Remote-Area-Monitoring/Remote-Area-Monitoring/3D_Models/Final_Design/wind_fin_pipeMnt.STL

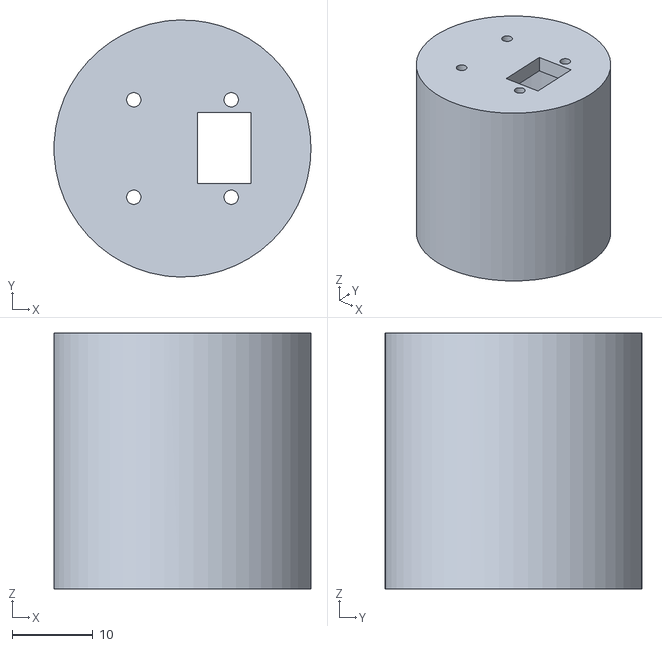
[picture p15: CAD file, 2022-09-11]
3D_Models/Final_Design/wind_fin_pipeMnt.STL
31.9 x 31.9 x 31.8
