Remote-Area-Monitoring/Remote-Area-Monitoring/3D_Models/Final_Design/aggregator_bottom.STL

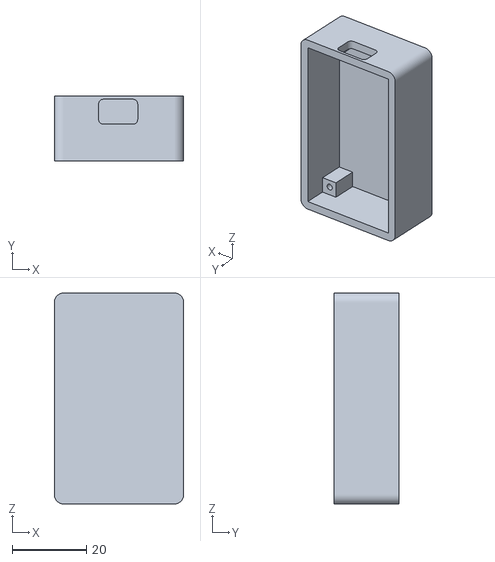
[picture p16: CAD file, 2022-09-11]
3D_Models/Final_Design/aggregator_bottom.STL
34.9 x 17.5 x 56.9
