Remote-Area-Monitoring/Remote-Area-Monitoring/3D_Models/Final_Design/cap2mag.STL

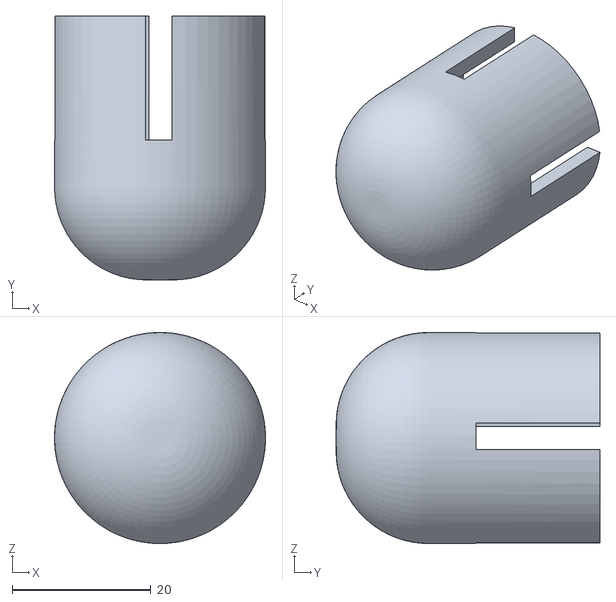
[picture p17: CAD file, 2022-09-11]
3D_Models/Final_Design/cap2mag.STL
30.5 x 38.1 x 30.5
