Remote-Area-Monitoring/Remote-Area-Monitoring/3D_Models/Final_Design/aggregator_top.STL

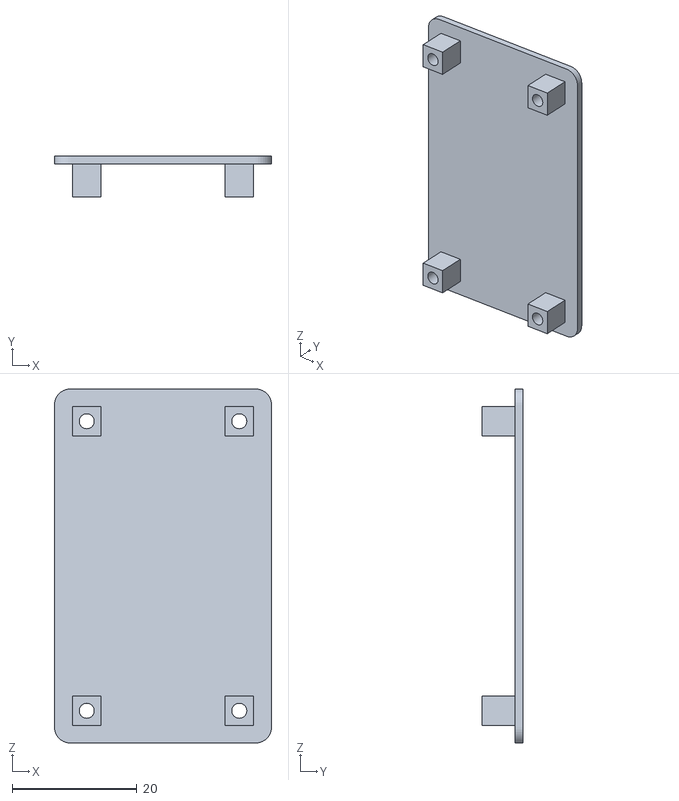
[picture p18: CAD file, 2022-09-11]
3D_Models/Final_Design/aggregator_top.STL
34.9 x 6.58 x 56.9
