Remote-Area-Monitoring/Remote-Area-Monitoring/3D_Models/Final_Design/lens_bezel.STL

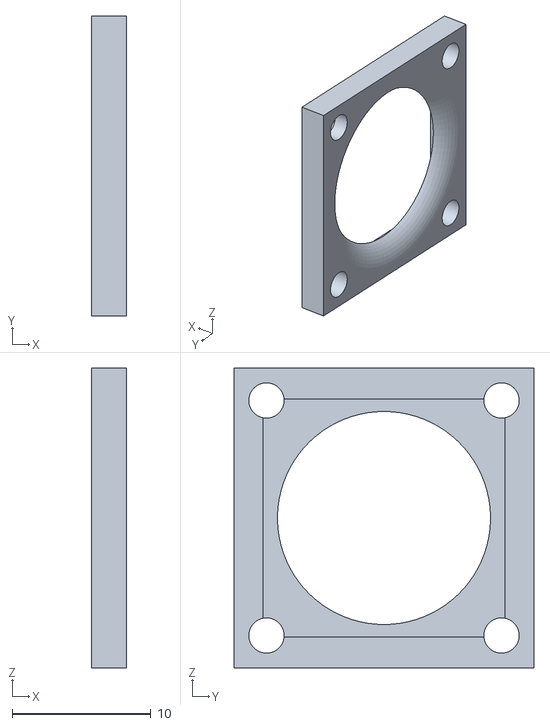
[picture p19: CAD file, 2022-09-11]
3D_Models/Final_Design/lens_bezel.STL
2.54 x 21.6 x 21.6
