Remote-Area-Monitoring/Remote-Area-Monitoring/3D_Models/Final_Design/an_fin_mount.STL

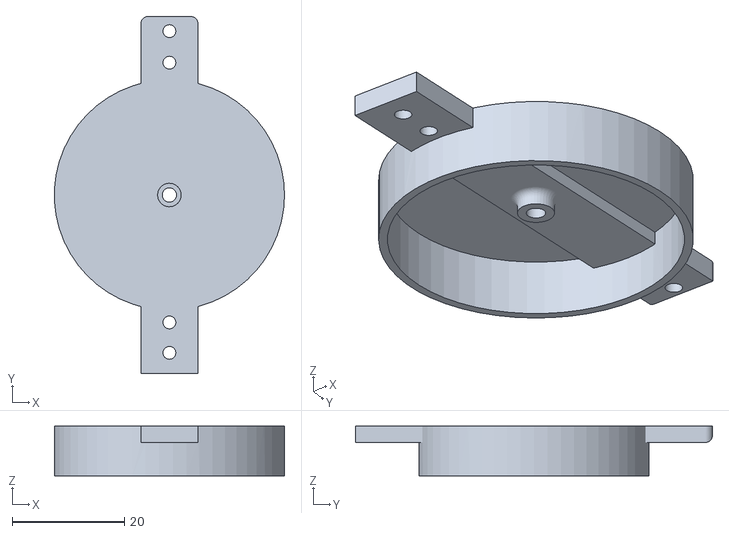
[picture p20: CAD file, 2022-09-11]
3D_Models/Final_Design/an_fin_mount.STL
40.9 x 63.5 x 8.89
