Remote-Area-Monitoring/Remote-Area-Monitoring/3D_Models/Final_Design/wind_fin_bearing.STL

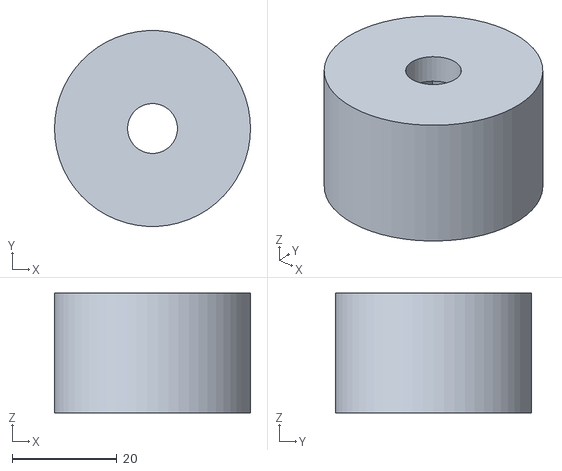
[picture p21: CAD file, 2022-09-11]
3D_Models/Final_Design/wind_fin_bearing.STL
37.4 x 37.3 x 22.9
