Remote-Area-Monitoring/Remote-Area-Monitoring/3D_Models/Final_Design/Part2^anemometer.STL

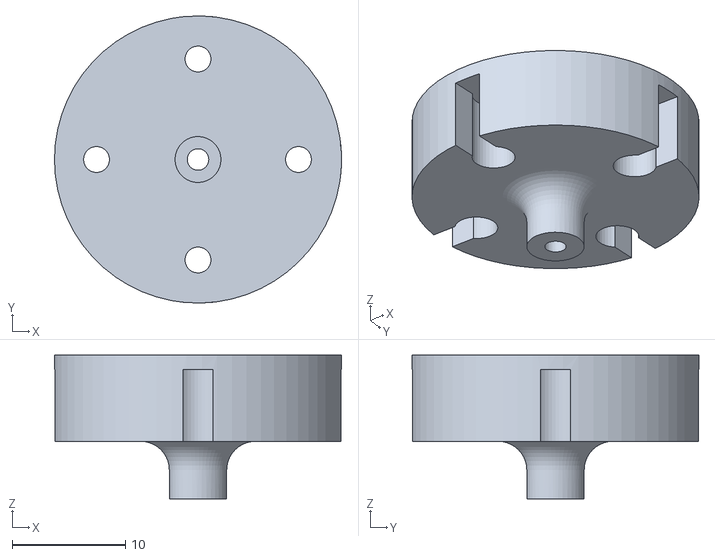
[picture p22: CAD file, 2022-09-11]
3D_Models/Final_Design/Part2^anemometer.STL
25.4 x 25.4 x 12.7
