Remote-Area-Monitoring/Remote-Area-Monitoring/3D_Models/Final_Design/solar bracket.STL

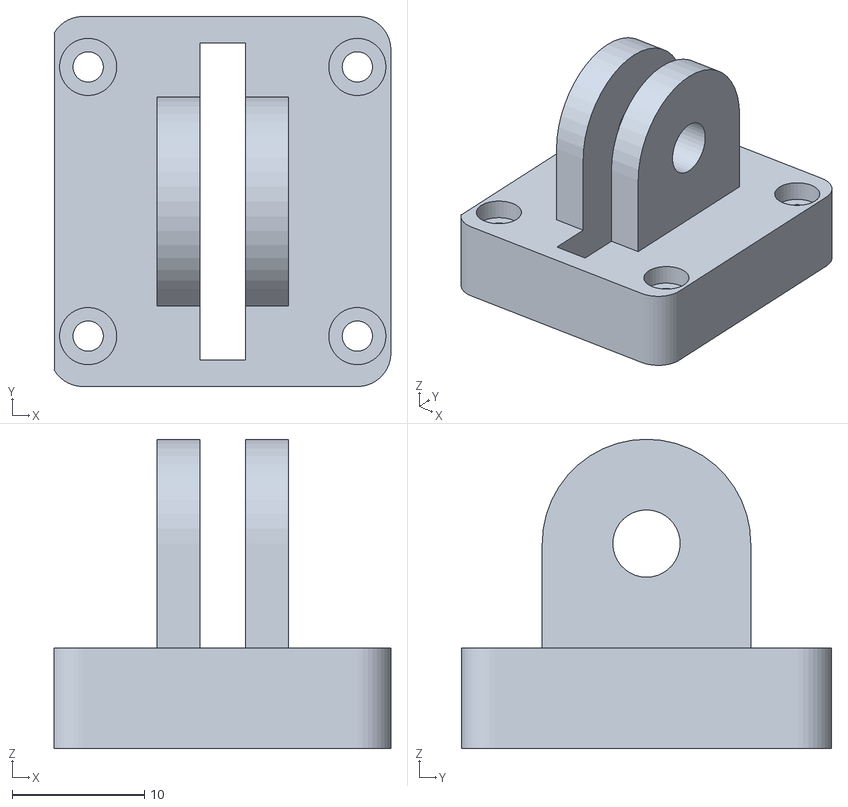
[picture p23: CAD file, 2022-09-11]
3D_Models/Final_Design/solar bracket.STL
25.4 x 27.9 x 23.4
