Remote-Area-Monitoring/Remote-Area-Monitoring/3D_Models/Final_Design/fin spacer.STL

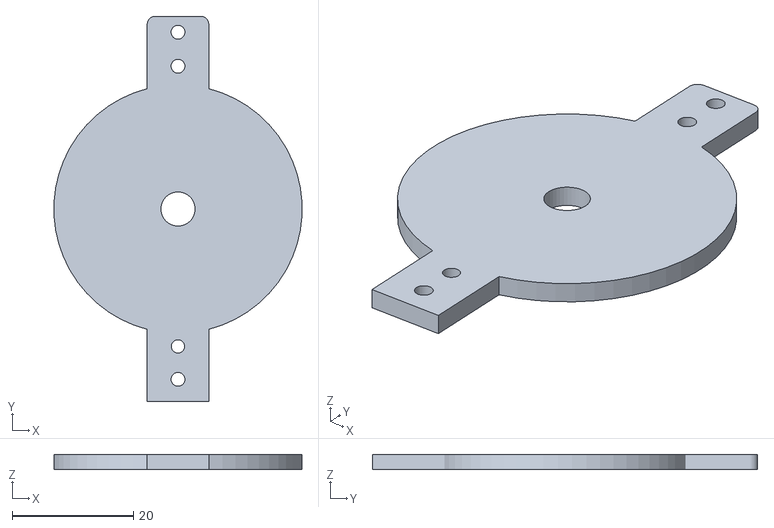
[picture p24: CAD file, 2022-09-11]
3D_Models/Final_Design/fin spacer.STL
40.9 x 63.5 x 2.54
