Remote-Area-Monitoring/Remote-Area-Monitoring/3D_Models/Final_Design/bottom_grill.STL

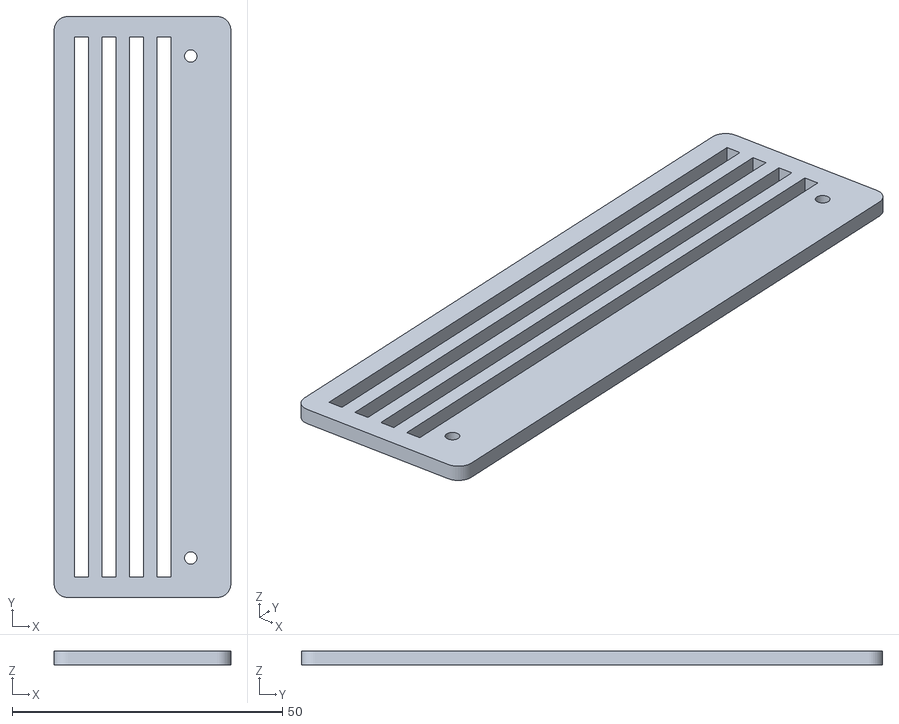
[picture p26: CAD file, 2022-09-11]
3D_Models/Final_Design/bottom_grill.STL
32.7 x 107.4 x 2.54
