Remote-Area-Monitoring/Remote-Area-Monitoring/3D_Models/Final_Design/pvcPipe mount.STL

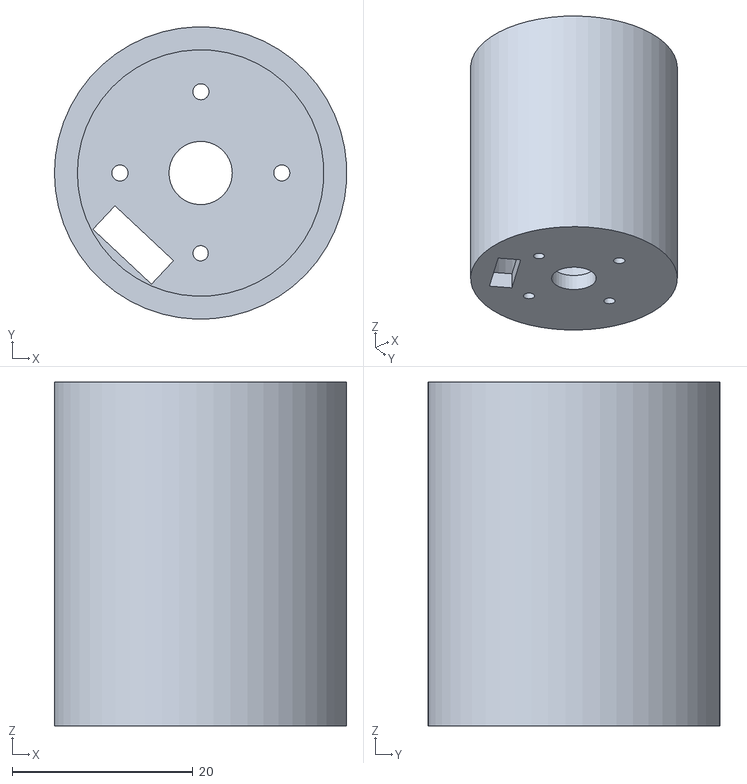
[picture p27: CAD file, 2022-09-11]
3D_Models/Final_Design/pvcPipe mount.STL
32.4 x 32.4 x 38.1
