Remote-Area-Monitoring/Remote-Area-Monitoring/3D_Models/Final_Design/Copy of Part1^anemometer rev4.STL

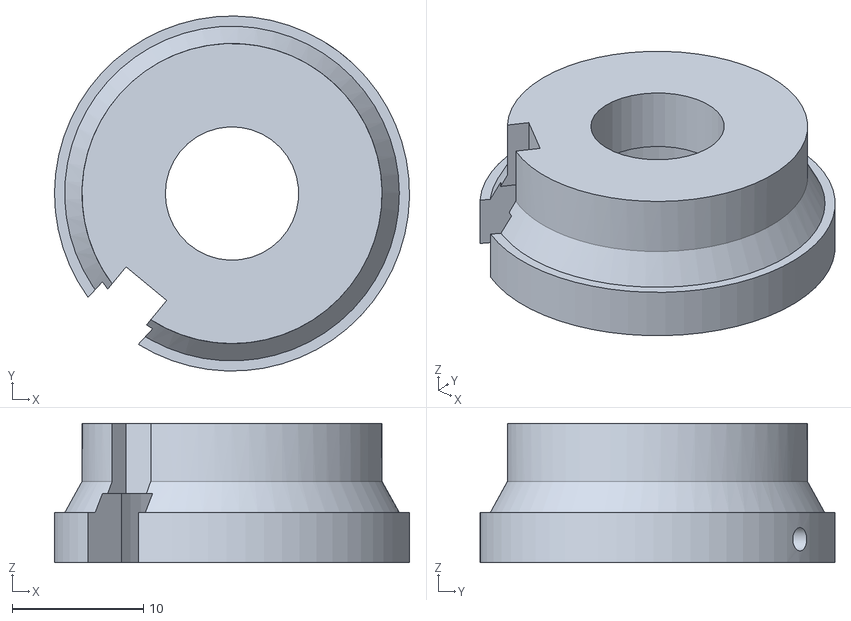
[picture p28: CAD file, 2022-09-11]
3D_Models/Final_Design/Copy of Part1^anemometer rev4.STL
27.0 x 27.0 x 10.6
