Remote-Area-Monitoring/Remote-Area-Monitoring/3D_Models/Final_Design/Part6^anemometer.STL

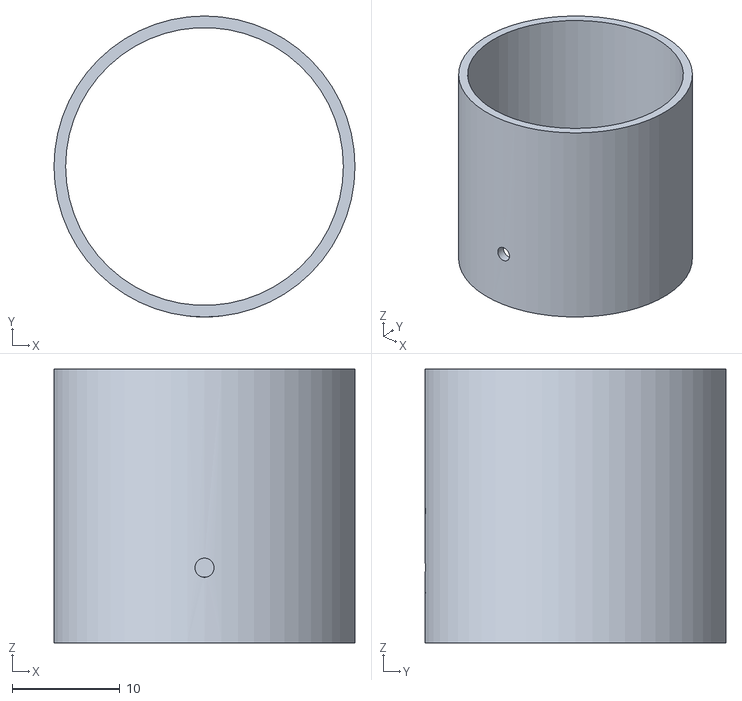
[picture p29: CAD file, 2022-09-11]
3D_Models/Final_Design/Part6^anemometer.STL
27.9 x 27.9 x 25.4
