Remote-Area-Monitoring/Remote-Area-Monitoring/3D_Models/Final_Design/top.STL

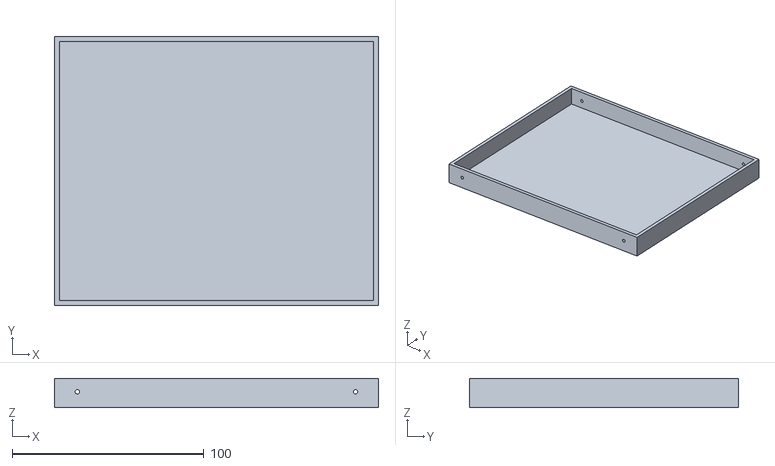
[picture p30: CAD file, 2022-09-11]
3D_Models/Final_Design/top.STL
169.0 x 140.2 x 15.2
