Remote-Area-Monitoring/Remote-Area-Monitoring/3D_Models/Final_Design/Part6^anemo rev3.STL

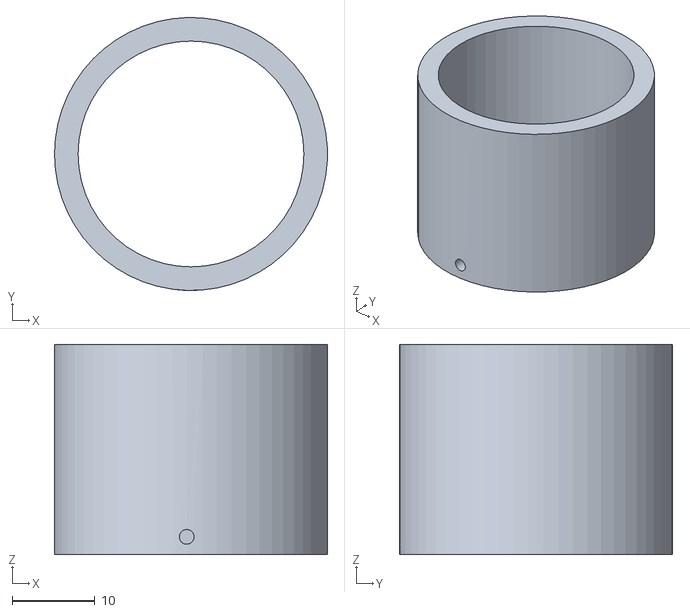
[picture p31: CAD file, 2022-09-11]
3D_Models/Final_Design/Part6^anemo rev3.STL
33.0 x 33.0 x 25.4
