Remote-Area-Monitoring/Remote-Area-Monitoring/3D_Models/Final_Design/wind_speed_cup.STL

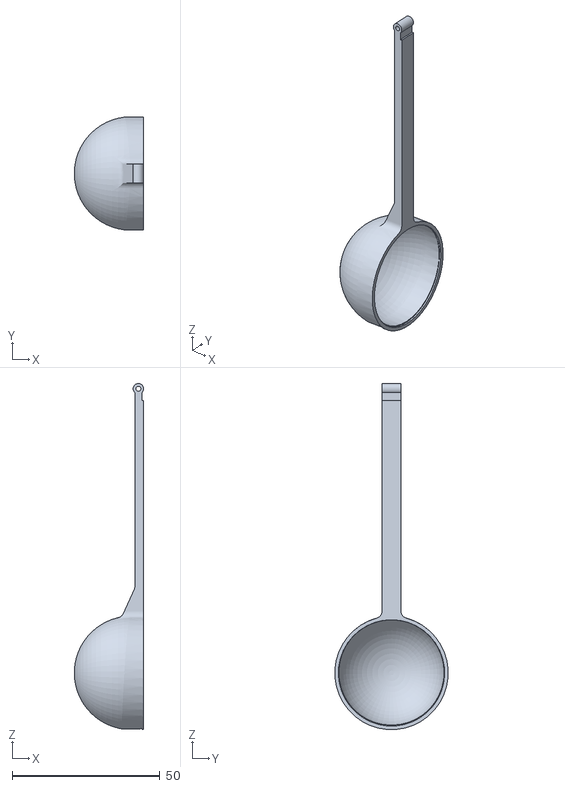
[picture p32: CAD file, 2022-09-11]
3D_Models/Final_Design/wind_speed_cup.STL
23.4 x 38.3 x 116.9
