Remote-Area-Monitoring/Remote-Area-Monitoring/3D_Models/Final_Design/solar_frame.STL

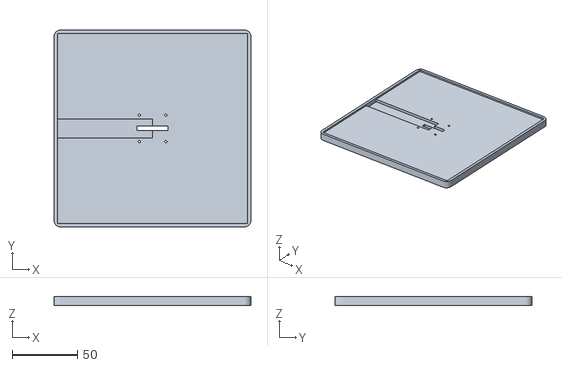
[picture p33: CAD file, 2022-09-11]
3D_Models/Final_Design/solar_frame.STL
150.9 x 150.9 x 6.65
