Remote-Area-Monitoring/Remote-Area-Monitoring/3D_Models/Final_Design/box bottom.STL

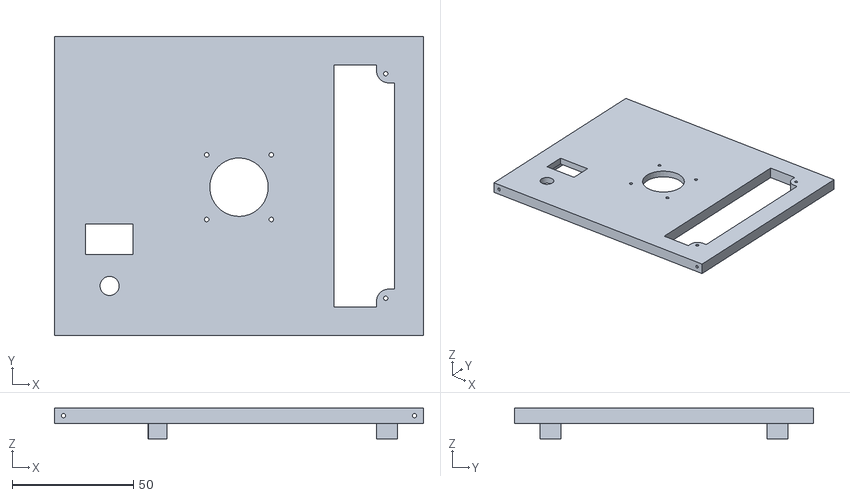
[picture p34: CAD file, 2022-09-11]
3D_Models/Final_Design/box bottom.STL
152.5 x 123.7 x 12.7
