Remote-Area-Monitoring/Remote-Area-Monitoring/3D_Models/Final_Design/Top_box.STL

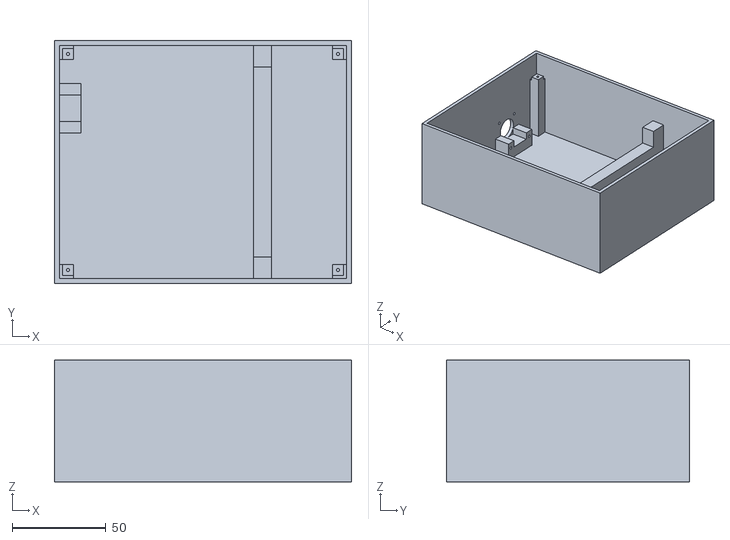
[picture p35: CAD file, 2022-09-11]
3D_Models/Final_Design/Top_box.STL
158.2 x 129.4 x 64.8
