Remote-Area-Monitoring/Remote-Area-Monitoring/source/prototype/current_monitor_mesh/current_monitor_aggregator/current_monitor_aggregator.ino

#include <painlessMesh.h>

#define   MESH_PREFIX     "ram"
#define   MESH_PASSWORD   "SeniorDesign1"
#define   MESH_PORT       5555


Scheduler userScheduler;
painlessMesh mesh;

void sendMessage();

Task taskSendMessage(TASK_SECOND * 1, TASK_FOREVER, &sendMessage);

void sendMessage()
{
  String message = "Echo sent from aggregator. Aggregator ID: ";
  message += mesh.getNodeId();
  mesh.sendBroadcast(message);
  // mesh.sendSingle(8043016, message);
  taskSendMessage.setInterval(TASK_SECOND * 10);
}

// Needed for painless library
void receivedCallback( uint32_t from, String &msg ) {
  Serial.printf("%s\n", msg.c_str());
}

void newConnectionCallback(uint32_t nodeId) {
    Serial.printf("--> startHere: New Connection, nodeId = %u\n", nodeId);
}

void changedConnectionCallback() {
  Serial.printf("Changed connections\n");
}

void nodeTimeAdjustedCallback(int32_t offset) {
    Serial.printf("Adjusted time %u. Offset = %d\n", mesh.getNodeTime(),offset);
}

void setup() {
  Serial.begin(115200);

//mesh.setDebugMsgTypes( ERROR | MESH_STATUS | CONNECTION | SYNC | COMMUNICATION | GENERAL | MSG_TYPES | REMOTE ); // all types on
  mesh.setDebugMsgTypes( ERROR | STARTUP );  // set before init() so that you can see startup messages

  mesh.init( MESH_PREFIX, MESH_PASSWORD, &userScheduler, MESH_PORT );
  mesh.onReceive(&receivedCallback);
  mesh.onNewConnection(&newConnectionCallback);
  mesh.onChangedConnections(&changedConnectionCallback);
  mesh.onNodeTimeAdjusted(&nodeTimeAdjustedCallback);

  userScheduler.addTask( taskSendMessage );
  taskSendMessage.enable();
}

void loop() {
  // it will run the user scheduler as well
  mesh.update();
}
