Remote-Area-Monitoring/Remote-Area-Monitoring/source/network/mesh.py

import serial
from serial import Serial
import json
import time
from source.util.timekeeper import Timestamps
from source.util.database import Database
from source.util.settings import Settings
from source.util.image import Image
import re
import sys
from time import sleep
from source.util.sun import Sunlight
from source.util.conversions import Convert


class Mesh:
    def __init__(self):
        self.ts = Timestamps()
        self.sun = Sunlight()
        self.image = Image()
        self.convert = Convert()
        self.config = Settings('general.config')
        self.nodes_config = Settings('nodes.config')
        self.nodes_db = Database(self.config.get_setting('databases', 'nodes_db_path'))
        self.sensor_data_db = Database(self.config.get_setting('databases', 'sensor_data_db_path'))
        self.images_db = Database(self.config.get_setting('databases', 'images_database_path'))
        self.port = self.config.get_setting('mesh_network', 'port')
        self.baud = self.config.get_int_setting('mesh_network', 'baud_rate')
        self.serial_timeout = self.config.get_int_setting('mesh_network', 'serial_timeout')
        self.ts = Timestamps()
        self.port = self.__get_connection()
        self.network_connection = self.is_connected()

    def __get_connection(self):
        # TODO: Move first try block to a function to check connection for any OS
        print(self.port)
        try:
            return Serial(self.port, self.baud, timeout=self.serial_timeout)
        except serial.SerialException:
            print('Windows COM port not found')
        try:
            return Serial('/dev/tty.usbserial-0001', self.baud, timeout=self.serial_timeout)
        except serial.SerialException:
            print('Mac COM port not found')
        print('No COM Ports Found')
        return None

    def get_topology(self):
        self.port.write('{"node_id":0, "message":"None"}'.encode())
        data = self.receive_json()
        if data is None:
            return data
        elif 'nodeId' not in data:
            data = self.receive_json()
        if data is None:
            return data
        if 'nodeId' not in data:
            return None
        # print(data)
        return data

    def get_connection_strength(self):
        self.port.write('{"node_id":2, "message":"None"}'.encode())
        data = self.receive_json()
        if data is None:
            return data
        elif 'connection_strength' not in data:
            data = self.receive_json()
        if data is None:
            return data
        if 'connection_strength' not in data:
            return None
        # print(data)
        return data

    def list_connected_nodes(self):
        topo = self.get_topology()
        # topo = {'nodeId': 2222635529, 'subs': [{'nodeId': 2222631473, 'subs': [{'nodeId': 2222817205}]}]}
        if topo is None:
            return None
        elif 'subs' not in topo:
            return None
        # nodes = list()
        topo.pop('nodeId')
        topo = json.dumps(topo)
        nodes = re.findall(r'\d+', topo)
        int_nodes = list()
        for node in nodes:
            try:
                int_nodes.append(int(node))
            except Exception as e:
                print('Invalid Node ID: ', node)
                print(e)
        return int_nodes

    def is_connected(self):
        if self.port is None:
            print('No com port found - not connected')
            return False
        startup = time.time()
        while True:
            topo = self.get_topology()
            if topo is not None:
                if 'subs' in topo:
                    return True
            if time.time() - startup > self.config.get_int_setting('mesh_network', 'connection_timeout'):
                print("TIMEOUT ERROR: Node Failed to Connect to Mesh")
                return False

    def send(self, node_id, message):
        msg = {'node_id': node_id, 'message': message}
        msg = json.dumps(msg).encode()
        self.port.write(msg)

    def receive_json(self):
        timeout = self.config.get_int_setting('mesh_network', 'receive_timeout')
        start = self.ts.get_timestamp()
        while True:
            if self.ts.get_timestamp() - start > timeout:
                return None
            try:
                message = self.port.readline()
                message = message.decode().split('*')[0]
                if '{' in message and '}' in message:
                    # print(message)
                    data = json.loads(message)
                    return data
            except Exception as e:
                print(e)
                continue

    def get_sensor_data(self, node_id):
        self.send(node_id, 'sensor_data')
        data = self.receive_json()
        if data is None:
            return data
        elif 'bus_voltage_V' not in data:
            data = self.receive_json()
        if data is None:
            return data
        elif 'bus_voltage_V' not in data:
            return None
        if 'wind_speed_raw' in data:
            data['wind_speed_mph'] = self.convert.raw_wind_speed_to_mph(data['wind_speed_raw'])
        elif 'wind_speed_mph' in data:
            if data['wind_speed_mph'] > 260:
                data['wind_speed_mph'] = 0
        if 'wind_direction_raw' in data:
            data['wind_direction'] = self.convert.raw_wind_direction_to_degrees(data['wind_direction_raw'])
        elif 'wind_direction' in data:
            if data['wind_direction'] > 360:
                data['wind_direction'] = 0
        if 'co2_ppm' in data:
            if data['co2_ppm'] < 400:
                data['co2_ppm'] = 400
        data_with_timestamp = {'timestamp': self.ts.get_timestamp()}
        data_with_timestamp.update(data)
        return data_with_timestamp

    def update_nodes_sensor_data(self):
        polling_enable = self.config.get_bool_setting('mesh_network', 'sensor_polling')
        sensors_last_updated = self.nodes_config.get_float_setting('connected_nodes', 'sensors_last_updated')
        sensors_polling_interval = self.config.get_float_setting('mesh_network', 'sensor_polling_interval')
        if polling_enable is False:
            print('Sensor Polling Disabled')
            return None
        elif self.ts.get_timestamp() - sensors_last_updated < sensors_polling_interval:
            return None
        self.nodes_config.set_setting('connected_nodes', 'sensors_last_updated', str(self.ts.get_timestamp()))
        print(self.get_topology())
        records = list()
        nodes = self.nodes_db.get_all()
        for node in nodes:
            connected_nodes = self.list_connected_nodes()
            if connected_nodes is None or len(connected_nodes) < 1:
                print('No nodes connected')
                continue
            if node['node_id'] not in connected_nodes:
                print('Node {} Not Connected'.format(node['node_id']))
                continue
            if node['status'] == 'active' and node['node_config']['sensors'] is True:
                data = self.get_sensor_data(node['node_id'])
                if data is not None:
                    print(data)
                    records.append(data)
                else:
                    # TODO: record error when node data is not found
                    print('Error: No data available for node', node['node_id'])
        self.sensor_data_db.insert_multiple(records)

    def receive_pixel_packets(self):
        # interesting note: The number of packets has no effect on the transfer speed, only the amount of data
        timeout = self.config.get_int_setting('mesh_network', 'image_timeout')
        start = self.ts.get_timestamp()
        packets = list()
        total_packets = None
        while True:
            if self.ts.get_timestamp() - start > timeout:
                return None
            try:
                raw_packets = self.port.readall()
                packets = raw_packets.decode()
                # print(packets)
                packets = packets.split('*')
                # for packet in packets:
                #     print(packet)
                data = list()
                packet_info = dict()
                for packet in packets:
                    try:
                        packet_data = json.loads(packet)
                    except Exception as e:
                        # print('failed to load json')
                        continue
                    if 'pixels' in packet_data:
                        # print(len(packet_data['pixels']))
                        data.append(packet_data)
                    elif 'total_packets_sent' in packet_data:
                        total_packets = packet_data['total_packets_sent']
                        packet_info = packet_data
                        print(packet_data)
                        print(total_packets)
                        print(len(data))
                        break
                if total_packets is not None:
                    if len(data) == (total_packets + 1):
                        print('All Packets Received')
                        print("Transmission Time:", self.ts.get_timestamp() - start)
                        return data, packet_info
                else:
                    print('Incomplete Pixel Data')
                    print('Expected: ', total_packets, 'Received: ', len(data))
                    print(data)
                    return None, None
            except Exception as e:
                print(e)
                continue

    def get_image_data(self, node_id):
        self.send(node_id, 'image')
        try:
            packet_data, packet_info = self.receive_pixel_packets()
        except TypeError:
            packet_data = None
            packet_info = None
        if packet_data is None:
            return None
        pixels = list()
        # for record in packet_data:
        #     print(record)
        # print(packet_info)
        # packet_data = self.receive_pixel_packets()
        packets = sorted(packet_data, key=lambda d: d['packet_number'])
        for packet in packets:
            pixels.extend(packet['pixels'])
        image_data = dict()
        image_data['node_id'] = node_id
        image_data['timestamp'] = self.ts.get_timestamp()
        image_data['total_packets_received'] = packet_info['total_packets_sent']
        image_data['pixels'] = pixels
        return image_data

    def update_nodes_image_data(self):
        polling_enable = self.config.get_bool_setting('mesh_network', 'image_polling')
        images_last_updated = self.nodes_config.get_float_setting('connected_nodes', 'images_last_updated')
        image_polling_interval = self.config.get_float_setting('mesh_network', 'image_polling_interval')
        if polling_enable is False:
            # print('Image Polling Disabled - Capture Suspended')
            return None
        elif self.ts.get_timestamp() - images_last_updated < image_polling_interval:
            # print('Image Capture Waiting - Seconds Remaining: ', self.ts.get_timestamp() - images_last_updated)
            return None
        # TODO: images can be saturated with green after overnight - need to create an init func for cam on arduino side
        # TODO: implement astral in place of suntime - sunset bug
        print(self.get_topology())
        self.nodes_config.set_setting('connected_nodes', 'images_last_updated', str(self.ts.get_timestamp()))
        attempts = self.config.get_int_setting('mesh_network', 'image_retry')
        retry_delay = self.config.get_int_setting('mesh_network', 'image_retry_delay')
        nodes = self.nodes_db.get_all()
        for node in nodes:
            if node['status'] == 'active' and node['node_config']['camera'] is True:
                for attempt in range(0, attempts):
                    # image_data = self.get_image_data(4144885065)
                    print('Getting Image Data for:', node['node_id'], )
                    image_data = self.get_image_data(node['node_id'])
                    # print(image_data)
                    if image_data is not None:
                        if self.image.validate_pixel_data(image_data['pixels']):
                            self.images_db.insert(image_data)
                            print('Image Saved to Database')
                            break
                        else:
                            print('Invalid Pixel Data - Attempt', attempt + 1, 'of', attempts)
                            sleep(retry_delay)
                            continue
                    else:
                        print('No Pixel Data - Attempt', attempt + 1, 'of', attempts)
                        sleep(retry_delay)
                        continue

    def update_connected_nodes(self):
        connected_nodes = self.list_connected_nodes()
        if connected_nodes is None:
            connected_nodes = '[]'
        else:
            connected_nodes = str(connected_nodes)
        self.nodes_config.set_setting('connected_nodes', 'node_ids', connected_nodes)
        self.nodes_config.set_setting('connected_nodes', 'last_updated', str(self.ts.get_timestamp()))
        self.nodes_config.set_setting('connected_nodes', 'topology', json.dumps(self.get_topology()))
        signal_strength = self.get_connection_strength()
        if signal_strength is not None:
            signal_strength = signal_strength['connection_strength']
        else:
            signal_strength = 0
        self.nodes_config.set_setting('connected_nodes', 'root_signal_strength', str(signal_strength))


    def write_image(self):
        pixels = self.get_image_data(4144885065)
        test_obj = dict()
        test_obj['pixel_data'] = pixels
        print(test_obj)
        print("test_obj size: {} bytes".format(sys.getsizeof(test_obj)))
        with open('test_img8.jpg', 'wb') as file:
            file.write(bytes(pixels))
        print('done')




def main():
    command = Mesh()
    # command.send(4144723677, 'This is a test message')
    # print(command.receive_json())
    # print(command.get_topology())
    # print(command.get_sensor_data(4144723677))
    # print(command.get_sensor_data(2222631473))
    # start = 0
    # cam_start = 0
    # while True:
    #     try:
    #         if time.time() - start > 5:
    #             start = time.time()
    #             db_nodes_detail = command.nodes_db.get_all()
    #             db_nodes = list()
    #             for node in db_nodes_detail:
    #                 db_nodes.append(node['node_id'])
    #             network_nodes = command.list_connected_nodes()
    #             nodes = set(db_nodes).intersection(network_nodes)
    #             print(command.get_topology())
    #             for node in nodes:
    #                 print('Getting Sensor Data for: ', node)
    #                 print(command.get_sensor_data(node))
    #             # print(command.get_sensor_data(4144723677)) # OG
    #             # print(command.get_sensor_data(4144717489)) # lighter
    #             # print(command.get_sensor_data(4146216805)) # medium
    #         # if time.time() - cam_start > 120:
    #         #     image_data = command.get_image_data(4144717489)
    #         #     if image_data is not None:
    #         #         if command.image.validate_pixel_data(image_data['pixels']):
    #         #             command.images_db.insert(image_data)
    #         #             print('Image Saved to Database')
    #         #         else:
    #         #             print(image_data)
    #         #             print('Invalid Pixel Data')
    #         #             continue
    #         #     else:
    #         #         print('No Pixel Data - Attempt')
    #         #         continue
    #     except KeyboardInterrupt:
    #         exit(0)
    # command.get_topology()
    # while True:
    #     command.update_nodes_image_data()
    #     sleep(90)

    # while True:
    #     command.get_topology()
    #     sleep(2)
    sensor_interval = 300
    cam_interval = 300
    connected_interval = 30
    sensor_start = 0
    cam_start = 0
    connected_start = 0
    # while True:
    #     try:
    #         if time.time() - connected_start > connected_interval:
    #             command.update_connected_nodes()
    #             connected_start = time.time()
    #         if time.time() - sensor_start > sensor_interval:
    #             print(command.get_topology())
    #             command.update_nodes_sensor_data()
    #             sensor_start = time.time()
    #         if time.time() - cam_start > cam_interval:
    #             print(command.get_topology())
    #             command.update_nodes_image_data()
    #             cam_start = time.time()
    #     except KeyboardInterrupt:
    #         exit(0)
    while True:
        try:
            if time.time() - connected_start > connected_interval:
                command.update_connected_nodes()
                connected_start = time.time()
            command.update_nodes_sensor_data()
            command.update_nodes_image_data()
        except KeyboardInterrupt:
            exit(0)


if __name__ == '__main__':
    main()
