Remote-Area-Monitoring/Remote-Area-Monitoring/source/prototype/basic_networking_painlessmesh/node/node.ino

#include <painlessMesh.h>

#define   MESH_PREFIX     "ram"
#define   MESH_PASSWORD   "SeniorDesign1"
#define   MESH_PORT       5555

// Prototypes
void receivedCallback( uint32_t from, String &msg );

painlessMesh  mesh;

void setup() {
  Serial.begin(115200);
    
  mesh.setDebugMsgTypes( ERROR | STARTUP | CONNECTION );  // set before init() so that you can see startup messages

  mesh.init( MESH_PREFIX, MESH_PASSWORD, MESH_PORT );
  mesh.onReceive(&receivedCallback);
}

void loop() {
  mesh.update();
}

void receivedCallback( uint32_t from, String &msg ) {
  Serial.printf("echoNode: Received from %u msg=%s\n", from, msg.c_str());
  String message = "Echo from node ID: ";
  message += mesh.getNodeId();
  mesh.sendSingle(from, message);
}
